IPB-Robotic-Club/transporter/models/SLDPRT/L298N Driver.STEP.SLDPRT

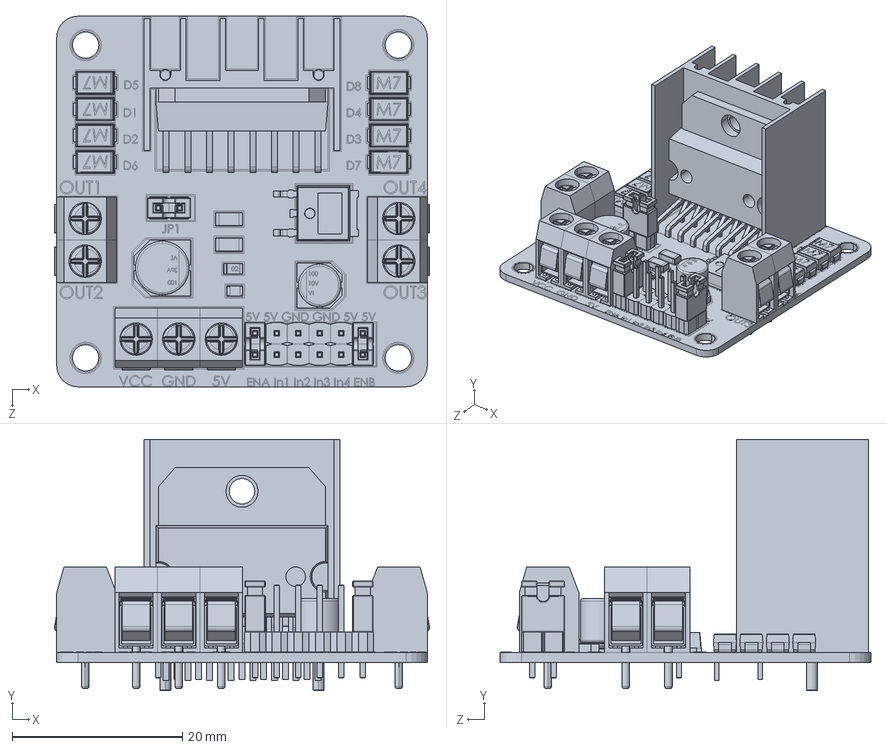
[picture p18: CAD file, 2025-04-23]
models/SLDPRT/L298N Driver.STEP.SLDPRT
44.0 x 29.5 x 43.5 mm
