IPB-Robotic-Club/transporter/models/SLDPRT/Gear Hand kanan.SLDPRT

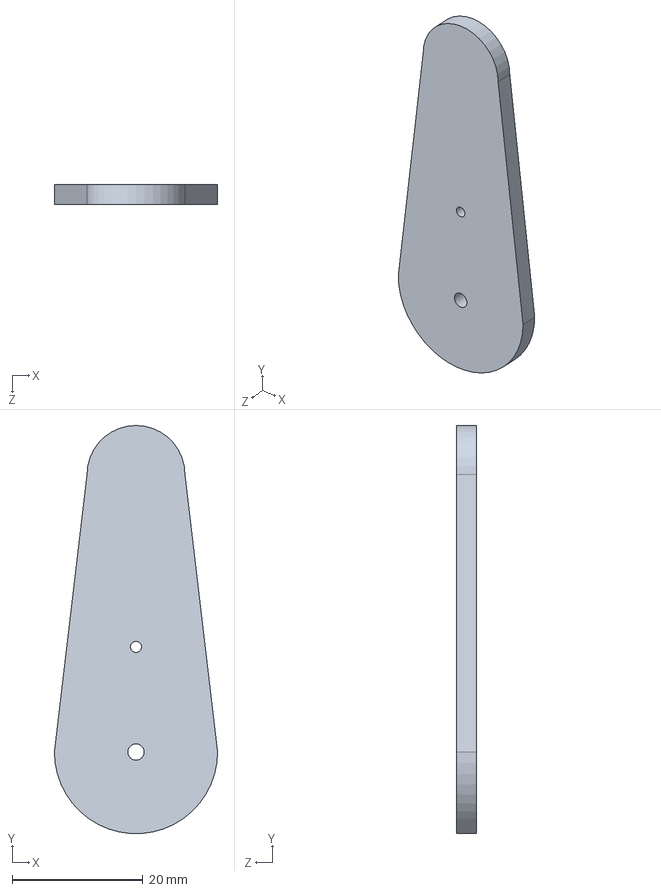
[picture p19: CAD file, 2025-04-23]
models/SLDPRT/Gear Hand kanan.SLDPRT
25.0 x 62.5 x 3.00 mm
