IPB-Robotic-Club/transporter/models/SLDPRT/Dudukan Grip.SLDPRT

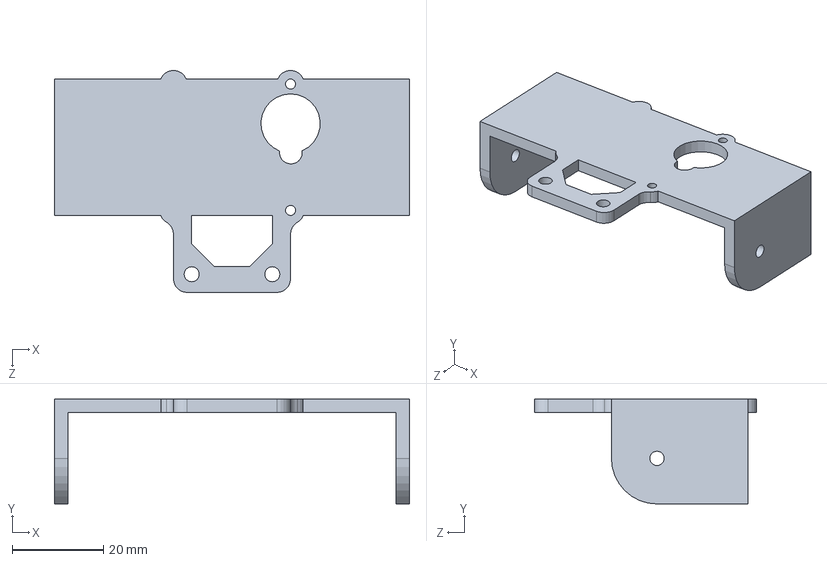
[picture p20: CAD file, 2025-04-23]
models/SLDPRT/Dudukan Grip.SLDPRT
77.8 x 23.0 x 48.7 mm
