IPB-Robotic-Club/transporter/models/SLDPRT/Body.SLDPRT

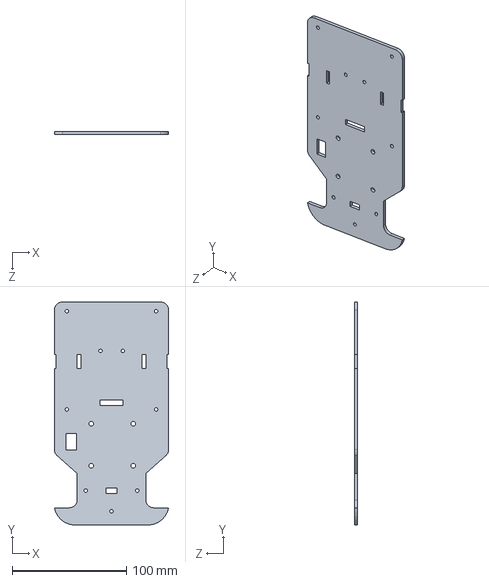
[picture p21: CAD file, 2025-04-23]
models/SLDPRT/Body.SLDPRT
100.0 x 195.0 x 3.00 mm
